N1UGK/PCUI_Public/Pocket Computer Programs/Casio PB-700/Graph/ReadMe.txt

(This is from the PB-770 Owners Manual)

GRAPH MAKING PROGRAM

This program draws various types of graphs with the plotter-printer
(FA-10 or F A-11). Up to 12 data items can be input. The range of data
is as follows.

I Value of data I 􀁥 1 E90

The program can draw beautiful band, bar, and line graphs, taking
advantage of the 4-color plotter-printer.

* This program is stored on the cassette tape which comes with the
FA-11 optional plotter-printer. It is also stored on the microcassette
tape which comes with the CM-1 optional microcassette tape recorder.
When the program is executed, the menu is displayed. First, data must be
entered. This can be done by pressing G].

The range of data is shown above. Data may be negative numerical data.
Up to 12 data items can be entered. After the 12th data item is entered,
the menu display automatically appears. To terminate the input in the
middle, press the􀁦 key without entering any numerical data.
Menu 2 is used to correct input data. Pressing (I] causes the first input
data to be displayed, and pressing the􀁦 key causes the next data to
appear. Pressing the 􀁧 and􀁦 keys causes the previous data to appear.
Input the correct data when data to be corrected appears.
Menu 3 is the routine to make graphs. Three kinds of graph names are
displayed by pressing @J. Select the type of graph by pressing(!], (I], or
@J. (Pressing 0causes return to the menu display.)
Type 1 is a band graph. The entire length of band represents 100%, with
the percentage of each data element represented by the length it occupies.
For easy recognition, the individual data elements are shown in
different colors and stripes. When the band graph is selected, negative
data causes the menu to be displayed.

Type 2 is a bar graph. The scale is automatically set according to the
size of input data. In this graph, positive values are output in green and
negative values are output in red.

Type 3 is a line graph. When@J is pressed, "Over previous graph?" is displayed.
If a bar graph has been drawn just before, a line graph can be
overwritten on the bar graph by pressing [!). If no bar graph has been
drawn or a line graph should not be overwritten on a bar graph, press CID.
In this case, the appropriate scale is automatically set and the line
graph is drawn.

Regardless of the type selected, the menu display appears after the
graph is drawn. The menu display also appears when no data is entered.
Note that starting the program again clears the existing data.

Menu 4 terminates program execution.

Menu 5 is provided to output the data to the plotter-printer. It can
also be used to output the total of data.
